SirBramble/The-Typeuwu/02 Firmware/Typeuwu_Firmware/keyboard-layout with leds.png

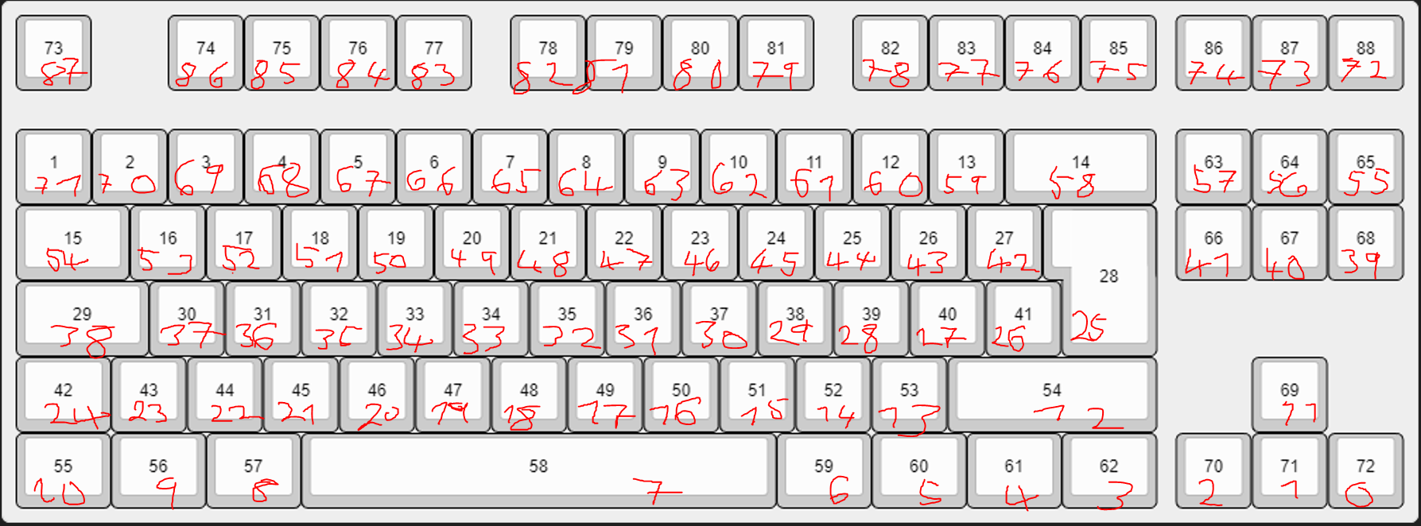
02 Firmware/Typeuwu_Firmware/keyboard-layout with leds.png
