SirBramble/The-Typeuwu/04 Pictures/20.jpeg

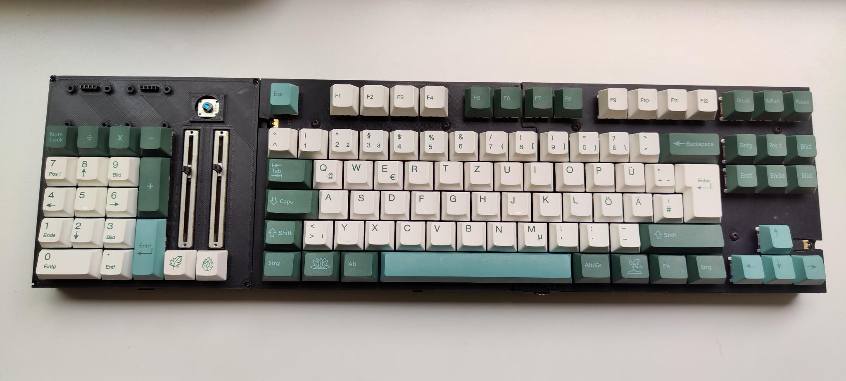
04 Pictures/20.jpeg
