SirBramble/The-Typeuwu/04 Pictures/The Typeuwu PCB back_rt.png

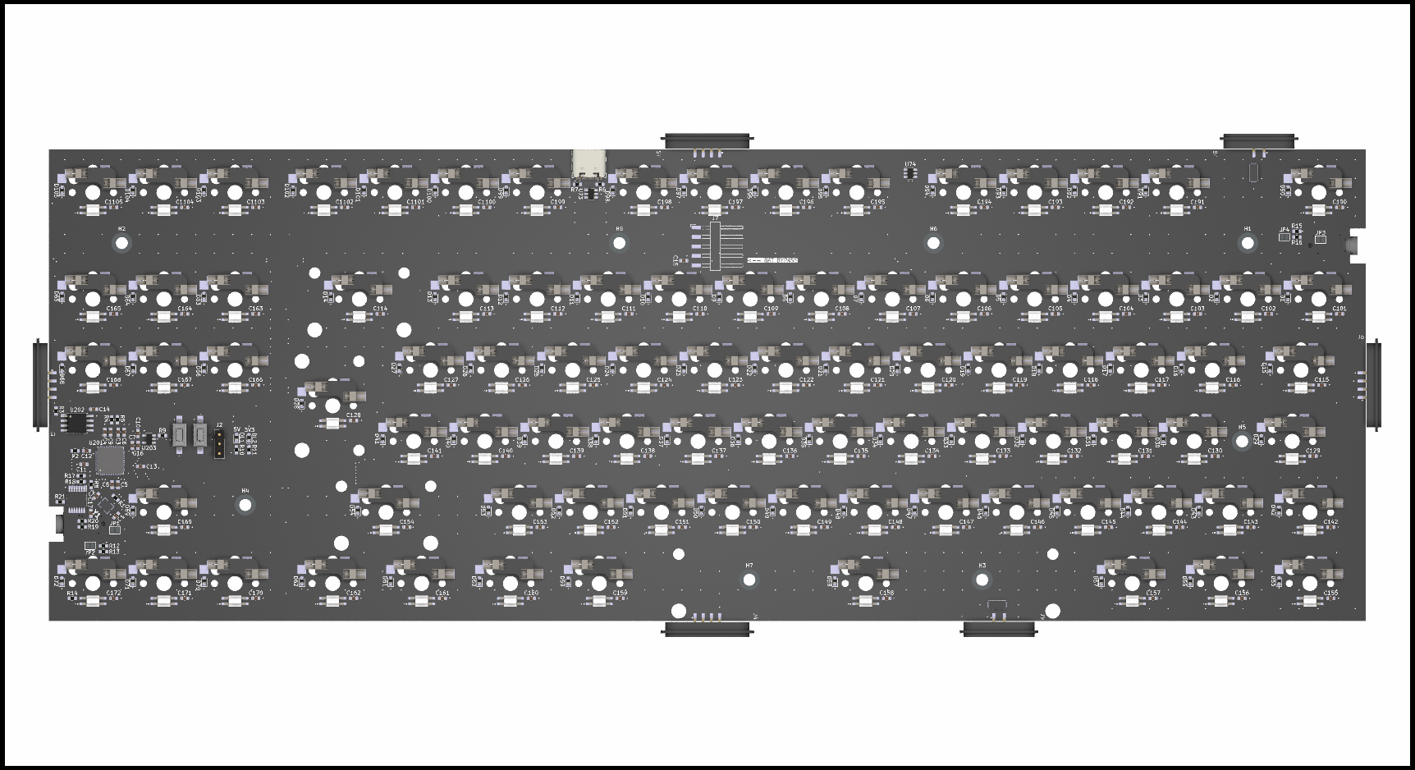
04 Pictures/The Typeuwu PCB back_rt.png
