SirBramble/The-Typeuwu/03 3D Files/Typeuwu Case/Buffer Plate 1.SLDPRT

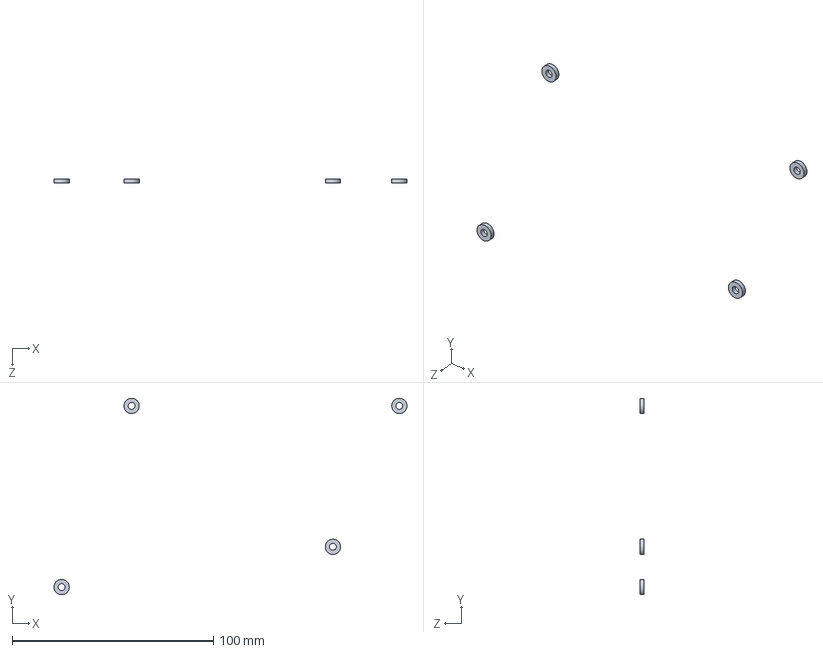
[picture p14: CAD file, 2025-01-14]
03 3D Files/Typeuwu Case/Buffer Plate 1.SLDPRT
175.4 x 97.6 x 2.00 mm
